YaoheWangEC/daq34001-rs485-voltmeter/software/voltmeter-f421g8u7/project/MDK_V5/voltmeter/bsp/lcd/lcdfont.c

#include "lcdfont.h"

#ifdef USE_NEW_FONT

const unsigned char ascii_1206[][12] =
{
{0x00,0x00,0x00,0x00,0x00,0x00,0x00,0x00,0x00,0x00,0x00,0x00},/*" ",0*/
/* (6 X 12 , @宋体 )*/

{0x00,0x00,0x04,0x04,0x04,0x04,0x04,0x00,0x00,0x04,0x00,0x00},/*"!",1*/
/* (6 X 12 , @宋体 )*/

{0x14,0x14,0x0A,0x00,0x00,0x00,0x00,0x00,0x00,0x00,0x00,0x00},/*""",2*/
/* (6 X 12 , @宋体 )*/

{0x00,0x00,0x0A,0x0A,0x1F,0x0A,0x0A,0x1F,0x0A,0x0A,0x00,0x00},/*"#",3*/
/* (6 X 12 , @宋体 )*/

{0x00,0x04,0x0E,0x15,0x05,0x06,0x0C,0x14,0x15,0x0E,0x04,0x00},/*"$",4*/
/* (6 X 12 , @宋体 )*/

{0x00,0x00,0x12,0x15,0x0D,0x15,0x2E,0x2C,0x2A,0x12,0x00,0x00},/*"%",5*/
/* (6 X 12 , @宋体 )*/

{0x00,0x00,0x04,0x0A,0x0A,0x36,0x15,0x15,0x29,0x16,0x00,0x00},/*"&",6*/
/* (6 X 12 , @宋体 )*/

{0x02,0x02,0x01,0x00,0x00,0x00,0x00,0x00,0x00,0x00,0x00,0x00},/*"'",7*/
/* (6 X 12 , @宋体 )*/

{0x10,0x08,0x08,0x04,0x04,0x04,0x04,0x04,0x08,0x08,0x10,0x00},/*"(",8*/
/* (6 X 12 , @宋体 )*/

{0x02,0x04,0x04,0x08,0x08,0x08,0x08,0x08,0x04,0x04,0x02,0x00},/*")",9*/
/* (6 X 12 , @宋体 )*/

{0x00,0x00,0x00,0x04,0x15,0x0E,0x0E,0x15,0x04,0x00,0x00,0x00},/*"*",10*/
/* (6 X 12 , @宋体 )*/

{0x00,0x00,0x00,0x08,0x08,0x3E,0x08,0x08,0x00,0x00,0x00,0x00},/*"+",11*/
/* (6 X 12 , @宋体 )*/

{0x00,0x00,0x00,0x00,0x00,0x00,0x00,0x00,0x02,0x02,0x01,0x00},/*",",12*/
/* (6 X 12 , @宋体 )*/

{0x00,0x00,0x00,0x00,0x00,0x3F,0x00,0x00,0x00,0x00,0x00,0x00},/*"-",13*/
/* (6 X 12 , @宋体 )*/

{0x00,0x00,0x00,0x00,0x00,0x00,0x00,0x00,0x00,0x02,0x00,0x00},/*".",14*/
/* (6 X 12 , @宋体 )*/

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
};
#endif
