YaoheWangEC/daq34001-rs485-voltmeter/software/voltmeter-f421g8u7/project/src/at32f421_wk_config.c

/* add user code begin Header */
/**
  **************************************************************************
  * @file     at32f421_wk_config.c
  * @brief    work bench config program
  **************************************************************************
  *                       Copyright notice & Disclaimer
  *
  * The software Board Support Package (BSP) that is made available to
  * download from Artery official website is the copyrighted work of Artery.
  * Artery authorizes customers to use, copy, and distribute the BSP
  * software and its related documentation for the purpose of design and
  * development in conjunction with Artery microcontrollers. Use of the
  * software is governed by this copyright notice and the following disclaimer.
  *
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
  **************************************************************************
  */
/* add user code end Header */

#include "at32f421_wk_config.h"

/* private includes ----------------------------------------------------------*/
/* add user code begin private includes */

/* add user code end private includes */

/* private typedef -----------------------------------------------------------*/
/* add user code begin private typedef */

/* add user code end private typedef */

/* private define ------------------------------------------------------------*/
/* add user code begin private define */

/* add user code end private define */

/* private macro -------------------------------------------------------------*/
/* add user code begin private macro */

/* add user code end private macro */

/* private variables ---------------------------------------------------------*/
/* add user code begin private variables */

/* add user code end private variables */

/* private function prototypes --------------------------------------------*/
/* add user code begin function prototypes */

/* add user code end function prototypes */

/* private user code ---------------------------------------------------------*/
/* add user code begin 0 */

/* add user code end 0 */

/**
  * @brief  system clock config program
  * @note   the system clock is configured as follow:
  *         system clock (sclk)   = (hext * pll_ns)/(pll_ms * pll_fr)
  *         system clock source   = HEXT_VALUE
  *         - lick                = on
  *         - lext                = off
  *         - hick                = on
  *         - hext                = off
  *         - hext                = HEXT_VALUE
  *         - sclk                = 100000000
  *         - ahbdiv              = 1
  *         - ahbclk              = 100000000
  *         - apb1div             = 1
  *         - apb1clk             = 100000000
  *         - apb2div             = 1
  *         - apb2clk             = 100000000
  *         - pll_ns              = 100
  *         - pll_ms              = 3
  *         - pll_fr              = 8
  *         - flash_wtcyc         = 3 cycle
  * @param  none
  * @retval none
  */
void wk_system_clock_config(void)
{
  /* reset crm */
  crm_reset();

  /* config flash psr register */
  flash_psr_set(FLASH_WAIT_CYCLE_3);

  /* enable lick */
  crm_clock_source_enable(CRM_CLOCK_SOURCE_LICK, TRUE);

  /* wait till lick is ready */
  while(crm_flag_get(CRM_LICK_STABLE_FLAG) != SET)
  {
  }

  /* enable hext */
  crm_clock_source_enable(CRM_CLOCK_SOURCE_HEXT, TRUE);

  /* wait till hext is ready */
  while(crm_hext_stable_wait() == ERROR)
  {
  }

  /* enable hick */
  crm_clock_source_enable(CRM_CLOCK_SOURCE_HICK, TRUE);

  /* wait till hick is ready */
  while(crm_flag_get(CRM_HICK_STABLE_FLAG) != SET)
  {
  }

  /* config pll clock resource */
  crm_pll_config2(CRM_PLL_SOURCE_HEXT, 100, 3, CRM_PLL_FR_8);

  /* enable pll */
  crm_clock_source_enable(CRM_CLOCK_SOURCE_PLL, TRUE);

  /* wait till pll is ready */
  while(crm_flag_get(CRM_PLL_STABLE_FLAG) != SET)
  {
  }

  /* config ahbclk */
  crm_ahb_div_set(CRM_AHB_DIV_1);

  /* config apb2clk */
  crm_apb2_div_set(CRM_APB2_DIV_1);

  /* config apb1clk */
  crm_apb1_div_set(CRM_APB1_DIV_1);

  /* select pll as system clock source */
  crm_sysclk_switch(CRM_SCLK_PLL);

  /* wait till pll is used as system clock source */
  while(crm_sysclk_switch_status_get() != CRM_SCLK_PLL)
  {
  }

  /* update system_core_clock global variable */
  system_core_clock_update();
}

/**
  * @brief  config periph clock
  * @param  none
  * @retval none
  */
void wk_periph_clock_config(void)
{
  /* enable dma1 periph clock */
  crm_periph_clock_enable(CRM_DMA1_PERIPH_CLOCK, TRUE);

  /* enable gpioa periph clock */
  crm_periph_clock_enable(CRM_GPIOA_PERIPH_CLOCK, TRUE);

  /* enable gpiob periph clock */
  crm_periph_clock_enable(CRM_GPIOB_PERIPH_CLOCK, TRUE);

  /* enable gpiof periph clock */
  crm_periph_clock_enable(CRM_GPIOF_PERIPH_CLOCK, TRUE);

  /* enable scfg periph clock */
  crm_periph_clock_enable(CRM_SCFG_PERIPH_CLOCK, TRUE);

  /* enable spi1 periph clock */
  crm_periph_clock_enable(CRM_SPI1_PERIPH_CLOCK, TRUE);

  /* enable usart1 periph clock */
  crm_periph_clock_enable(CRM_USART1_PERIPH_CLOCK, TRUE);

  /* enable usart2 periph clock */
  crm_periph_clock_enable(CRM_USART2_PERIPH_CLOCK, TRUE);

  /* enable i2c1 periph clock */
  crm_periph_clock_enable(CRM_I2C1_PERIPH_CLOCK, TRUE);

  /* enable i2c2 periph clock */
  crm_periph_clock_enable(CRM_I2C2_PERIPH_CLOCK, TRUE);
}

/**
  * @brief  nvic config
  * @param  none
  * @retval none
  */
void wk_nvic_config(void)
{
  nvic_priority_group_config(NVIC_PRIORITY_GROUP_4);

  NVIC_SetPriority(MemoryManagement_IRQn, NVIC_EncodePriority(NVIC_GetPriorityGrouping(), 0, 0));
  NVIC_SetPriority(BusFault_IRQn, NVIC_EncodePriority(NVIC_GetPriorityGrouping(), 0, 0));
  NVIC_SetPriority(UsageFault_IRQn, NVIC_EncodePriority(NVIC_GetPriorityGrouping(), 0, 0));
  NVIC_SetPriority(SVCall_IRQn, NVIC_EncodePriority(NVIC_GetPriorityGrouping(), 0, 0));
  NVIC_SetPriority(DebugMonitor_IRQn, NVIC_EncodePriority(NVIC_GetPriorityGrouping(), 0, 0));
  NVIC_SetPriority(PendSV_IRQn, NVIC_EncodePriority(NVIC_GetPriorityGrouping(), 0, 0));
  NVIC_SetPriority(SysTick_IRQn, NVIC_EncodePriority(NVIC_GetPriorityGrouping(), 15, 0));
  nvic_irq_enable(DMA1_Channel5_4_IRQn, 0, 0);
  nvic_irq_enable(USART2_IRQn, 0, 0);
}

/* add user code begin 1 */

/* add user code end 1 */
