YaoheWangEC/daq34001-rs485-voltmeter/software/voltmeter-f421g8u7/project/src/wk_system.c

/* add user code begin Header */
/**
  **************************************************************************
  * @file     wk_system.c
  * @brief    work bench config program
  **************************************************************************
  *                       Copyright notice & Disclaimer
  *
  * The software Board Support Package (BSP) that is made available to
  * download from Artery official website is the copyrighted work of Artery.
  * Artery authorizes customers to use, copy, and distribute the BSP
  * software and its related documentation for the purpose of design and
  * development in conjunction with Artery microcontrollers. Use of the
  * software is governed by this copyright notice and the following disclaimer.
  *
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
  **************************************************************************
  */
/* add user code end Header */

#include "wk_system.h"

#define STEP_DELAY_MS                    (uint32_t)(50)
#define TICK_COUNT_MAX                   (uint32_t)(0xFFFFFF)
#define TICK_COUNT_VALUE                 (SysTick->VAL)

/* global variable */
volatile uint32_t ticks_count_us;

/**
  * @brief  this function provides minimum delay (in microsecond).
  * @param  delay: specifies the delay time length, in microsecond.
  * @retval none
  */
__WEAK void wk_delay_us(uint32_t delay)
{
  uint32_t delay_ticks, pre_ticks, cur_ticks, delta;
  delay_ticks = delay * ticks_count_us;

  pre_ticks = TICK_COUNT_VALUE;
  do
  {
    cur_ticks = TICK_COUNT_VALUE;
    /* count down */
    delta = (cur_ticks <= pre_ticks) ? (pre_ticks - cur_ticks) : ((TICK_COUNT_MAX - cur_ticks) + pre_ticks + 1);
  } while(delta < delay_ticks);
}

/**
  * @brief  this function provides minimum delay (in milliseconds).
  * @param  delay variable specifies the delay time length, in milliseconds.
  * @retval none
  */
__WEAK void wk_delay_ms(uint32_t delay)
{
  while(delay)
  {
    if(delay > STEP_DELAY_MS)
    {
      wk_delay_us(STEP_DELAY_MS * 1000);
      delay -= STEP_DELAY_MS;
    }
    else
    {
      wk_delay_us(delay * 1000);
      delay = 0;
    }
  }
}

/**
  * @brief  this function configures the source of the time base.
  * @param  none
  * @retval none
  */
__WEAK void wk_timebase_init(void)
{
  crm_clocks_freq_type crm_clocks;
  uint32_t frequency = 0;

  /* get crm_clocks */
  crm_clocks_freq_get(&crm_clocks);

  frequency = crm_clocks.ahb_freq / 8;

  /* config systick clock source */
  systick_clock_source_config(SYSTICK_CLOCK_SOURCE_AHBCLK_DIV8);
  ticks_count_us = (frequency / 1000000U);
  /* system tick config */
  TICK_COUNT_VALUE = 0UL;
  SysTick->LOAD = TICK_COUNT_MAX;
  SysTick->CTRL |= SysTick_CTRL_ENABLE_Msk;
}

/* support printf function, usemicrolib is unnecessary */
#if (__ARMCC_VERSION > 6000000)
  __asm (".global __use_no_semihosting\n\t");
  void _sys_exit(int x)
  {
    UNUSED(x);
  }
  /* __use_no_semihosting was requested, but _ttywrch was */
  void _ttywrch(int ch)
  {
    UNUSED(ch);
  }
  FILE __stdout;
#else
 #ifdef __CC_ARM
  #pragma import(__use_no_semihosting)
  struct __FILE
  {
    int handle;
  };
  FILE __stdout;
  void _sys_exit(int x)
  {
    UNUSED(x);
  }
  /* __use_no_semihosting was requested, but _ttywrch was */
  void _ttywrch(int ch)
  {
    UNUSED(ch);
  }
 #endif
#endif

#if defined (__GNUC__) && !defined (__clang__)
  #define PUTCHAR_PROTOTYPE int __io_putchar(int ch)
#else
  #define PUTCHAR_PROTOTYPE int fputc(int ch, FILE *f)
#endif

/**
  * @brief  retargets the c library printf function to the usart.
  * @param  none
  * @retval none
  */
PUTCHAR_PROTOTYPE
{
#if !defined (__GNUC__) || defined (__clang__)
  UNUSED(f);
#endif
  while(usart_flag_get(USART1, USART_TDBE_FLAG) == RESET);
  usart_data_transmit(USART1, (uint16_t)ch);
  while(usart_flag_get(USART1, USART_TDC_FLAG) == RESET);
  return ch;
}

#if (defined (__GNUC__) && !defined (__clang__)) || (defined (__ICCARM__))
#if defined (__GNUC__) && !defined (__clang__)
int _write(int fd, char *pbuffer, int size)
#elif defined ( __ICCARM__ )
#pragma module_name = "?__write"
int __write(int fd, char *pbuffer, int size)
#endif
{
  UNUSED(fd);
  for(int i = 0; i < size; i ++)
  {
    while(usart_flag_get(USART1, USART_TDBE_FLAG) == RESET);
    usart_data_transmit(USART1, (uint16_t)(*pbuffer++));
    while(usart_flag_get(USART1, USART_TDC_FLAG) == RESET);
  }

  return size;
}
#endif
