YaoheWangEC/daq34001-rs485-voltmeter/software/voltmeter-f421g8u7/project/MDK_V5/voltmeter/bsp/lcd/lcdfont.h

#ifndef __LCDFONT_H_
#define __LCDFONT_H_

#define USE_NEW_FONT 1


extern const unsigned char ascii_1206[][12];

extern const unsigned char ascii_1608[][16];

extern const unsigned char ascii_2412[][48];

extern const unsigned char ascii_3216[][64];

#endif
