YaoheWangEC/daq34001-rs485-voltmeter/software/voltmeter-f421g8u7/project/MDK_V5/voltmeter/command/command_handler.h

#ifndef COMMAND_HANDLER_H
#define COMMAND_HANDLER_H

#include <stdint.h>

char* lscmd_handler(int argc, char **argv);

char* echo_handler(int argc, char **argv);

char* volt_handler(int argc, char **argv);

char* range_handler(int argc, char **argv);

char* calib_handler(int argc, char **argv);

#endif // COMMAND_HANDLER_H
